RattleBrattle/SmartPSU/Code/Smart Power Supply (SPS) V2.0/ATmega32_DIO/DIO_REG.h

/*
 * DIO_REG.h
 *
 *  Created on: Aug 14, 2024
 *      Author: baselses
 */

#ifndef DIO_REG_H_
#define DIO_REG_H_

/*Group A */
#define  PORTA_REG          *((volatile u8*)0x3B)
#define  DDRA_REG           *((volatile u8*)0x3A)
#define  PINA_REG           *((volatile u8*)0x39)

/*Group B */
#define  PORTB_REG          *((volatile u8*)0x38)
#define  DDRB_REG           *((volatile u8*)0x37)
#define  PINB_REG           *((volatile u8*)0x36)

/*Group C */
#define  PORTC_REG          *((volatile u8*)0x35)
#define  DDRC_REG           *((volatile u8*)0x34)
#define  PINC_REG           *((volatile u8*)0x33)

/*Group D */
#define PORTD_REG           *((volatile u8*)0x32)
#define  DDRD_REG           *((volatile u8*)0x31)
#define  PIND_REG           *((volatile u8*)0x30)

#endif /* DIO_REG_H_ */
